bligede/bmt-avanza-iot-testing/ProjectDocs/BACKLOG.md

# BACKLOG: Alat Diagnostik CAN BMT

**Last updated:** 29 Sep 2026 WITA

Semua yang **belum bisa** atau **belum layak** dikerjakan sekarang, beserta apa
yang membukanya. Satu tempat, supaya tidak ada yang hilang di sela catatan.

Yang **sedang** dikerjakan dan yang **berikutnya** ada di
`agent-documentation/08-HANDOFF-CHECKLIST.md`. Pertanyaan yang menunggu jawaban
orang, bukan pekerjaan, tetap di berkas itu juga. Backlog ini isinya pekerjaan.

Status yang dipakai:

| Status | Artinya |
|---|---|
| **Siap** | tidak ada yang menghalangi, tinggal dikerjakan |
| **Menunggu akses** | butuh kendaraan, perangkat keras, atau jaringan tertentu |
| **Menunggu keputusan** | butuh jawaban operator BMT lebih dulu |
| **Ditahan sengaja** | bisa dikerjakan, tetapi sengaja tidak, dan alasannya ditulis |

---

## A. Beban perangkat dan kehilangan frame

Semuanya bersumber dari satu sebab yang sama: interupsi CAN berada di flash,
jadi setiap penulisan flash mematikan cache instruksi dan FIFO controller
meluap. Terukur 14,8 % hilang saat merekam ke flash, 0,0 % saat flash menganggur.
Rinciannya di `docs/evidence/00-umum/frame-loss.md`.

### B-01. Filter penerimaan hardware TWAI · **Ditahan sengaja**

Menyaring di controller, sebelum interupsi jalan, jadi frame yang tidak
diinginkan tidak menimbulkan kerja sama sekali.

Sudah diukur pada rekaman `gelora-004` yang sebenarnya:

| | |
|---|---|
| Lima identifier yang dipakai TDS | 26,3 % dari lalu lintas bus |
| Mask tunggal yang memuat kelimanya | meloloskan **13 dari 34** identifier |
| Beban setelah disaring | 36,4 % dari bus, jadi turun 63,6 % |

Mask TWAI memilih **pola bit**, bukan daftar, jadi tidak mungkin menyaring tepat
lima identifier. Itu sifat perangkat kerasnya, bukan kekurangan implementasi.

**Kenapa ditahan:** mematikan perekaman sudah memberi kehilangan **nol** tanpa
menyentuh kode sama sekali, sedangkan filter ini hanya memberi 63,6 % dan
membayarnya dengan rekaman yang **tidak lagi lengkap**. Satu-satunya kasus
pemakaiannya adalah sesi perekaman panjang yang memang hanya butuh sinyal TDS,
dan kasus itu belum ada.

**Yang membukanya:** kebutuhan merekam lama dengan hanya sinyal TDS, misalnya
uji ketahanan unit armada. Kalau dikerjakan, **wajib** ada cap di header berkas
rekaman yang menyatakan filter aktif dan mask-nya, supaya analisis berikutnya
tidak diam-diam mengira rekaman itu utuh.

### B-02. Format rekaman biner, bukan teks · **Siap**

Satu frame sekarang memakan sekitar 44 byte teks. Bentuk biner sekitar 17 byte,
jadi lalu lintas flash turun 2,6 kali dan jeda cache ikut turun sebanding.

Lebih baik daripada B-01 untuk kasus yang sama, karena **tidak membuang satu
frame pun**. Biayanya: format berubah, `capture_to_webcan.py` dan seluruh alat
pembaca harus menyesuaikan, dan berkas lama harus tetap terbaca.

**Kenapa belum:** belum ada sesi yang menuntutnya. Kalau pemetaan Wuling ternyata
menuntut perekaman flash yang panjang, ini yang dikerjakan lebih dulu, bukan B-01.

### B-03. Bangun ulang framework dengan `CONFIG_TWAI_ISR_IN_IRAM=y` · **Ditahan sengaja**

Perbaikan tepat di akar masalah: interupsi CAN pindah ke IRAM, dan penulisan
flash berhenti mengganggunya.

**Kenapa ditahan:** tidak bisa dengan paket Arduino siap pakai, perlu ESP-IDF
dengan Arduino sebagai komponen, dan itu mengubah seluruh cara build. Kalau arah
Orange Pi 5 (D-007) jadi, seluruh pekerjaan ini terbuang.

**Yang membukanya:** keputusan bahwa ESP32 tetap dipakai untuk jangka panjang.

### B-04. Slot microSD pada papan rev B · **Menunggu keputusan**

Menulis ke SD lewat SPI tidak mematikan cache instruksi, jadi interupsi CAN
tetap jalan. Sekaligus menghapus batas 12 MB.

**Yang membukanya:** keputusan rev A difabrikasi apa adanya atau langsung lompat
ke rev B. Rev A belum pernah difabrikasi, jadi masih sempat.

---

## B. Pemetaan kendaraan

### B-05. Pemetaan sinyal Wuling armada · **Menunggu akses**

Penghalang terbesar yang tersisa di seluruh project, dan satu-satunya yang
menghalangi `project-mdt-tds` bergerak.

Metodenya sudah terbukti, prosedurnya sudah tertulis, firmware tinggal ditambah
satu env kendaraan. Yang kurang **hanya akses ke kendaraannya**.

Persiapan ada di `08-HANDOFF-CHECKLIST.md` butir 3.

### B-06. Uji jalan Honda HR-V · **Menunggu akses**

Kandidat 8 Sep 2026 belum pernah diuji sambil berjalan, jadi statusnya sama
dengan status Gelora E sebelum 23 Sep: cocok di atas kertas, belum terbukti.

Bus HR-V sekitar 1.000 frame per detik, jadi kehilangan saat merekam ke flash
mencapai 22 sampai 26 persen. Sesi berikutnya **wajib** memakai aliran WiFi.

### B-07. Dokumen bukti untuk `gelora-002`, `gelora-003`, dan `gelora-005` · **Siap**

Tiga rekaman dari 22 September malam, 216.454 + 200.389 + 213.979 frame,
tersimpan di `captures/` tanpa dokumen bukti sama sekali. Sebagian angkanya
sudah dipakai di `frame-loss.md`, jadi rekamannya bukan sampah, hanya tidak
punya jejak.

Ketiganya tumpang tindih dan harus dibaca bersama: dua yang pertama dialirkan
ke laptop, yang ketiga ditulis ke flash alat. Itulah sisi kanan dan kiri dari
perbandingan 14,8 % lawan 0,0 %.

`gelora-005` baru ditarik 23 Sep 2026 dan **nyaris hilang**, lihat
`captures/gelora-005/RUN-SHEET.md`.

### B-08. Sinyal Gelora E yang belum selesai · **Siap**

| Yang belum selesai | Keadaannya |
|---|---|
| Nomor sel tertinggi `0x0CFF7D03` b2 | b2 = 44 sedangkan sel 3991 mV ada di posisi 46. Nilainya terbukti, penomorannya belum |
| SOH `0x0CFF7E03` b1 | tidak pernah berubah, jadi belum teruji sama sekali |
| Suhu controller `0x0CFF1601` b2 | **gugur**, tidak bergerak 47 menit termasuk saat arus 133 A. Perlu dicari ulang di identifier lain |
| Resistansi isolasi | tidak ada di 34 identifier mana pun. Kemungkinan hanya keluar lewat permintaan diagnostik, lihat B-14 |

### B-09. Rumus untuk frame multiplex · **Siap**

Tegangan 90 sel dan suhu 30 sensor berbentuk multiplex: satu byte indeks lalu
tiga nilai 16-bit. Mesin rumus di dashboard hanya bisa menyatakan satu frame
tunggal, jadi keduanya hanya bisa dinamai, tidak bisa ditampilkan sebagai angka
di panel Vehicle.

Untuk TDS ini belum penting. Untuk melihat ketidakseimbangan baterai di lapangan,
ini yang dibutuhkan.

---

## C. Dashboard

### B-10. Mode terang untuk dibaca di bawah matahari · **Siap**

Halaman sekarang gelap sepenuhnya. Di kabin terang siang hari, permukaan gelap
memantulkan lebih banyak daripada permukaan terang. Belum pernah diuji di
kendaraan pada siang hari, jadi ini dugaan, bukan keluhan terukur.

**Sebelum dikerjakan:** ukur dulu. Satu sesi siang hari sudah cukup untuk tahu
apakah ini masalah nyata.

### B-11. Panel Live Frames · **Menunggu keputusan**

Endpoint `/api/frames` ada, berjalan, dan menyajikan 60 frame terakhir, tetapi
**halaman tidak pernah memakainya**. Dua pilihan yang sama-sama sah: pakai
sebagai panel debug, atau hapus endpoint-nya karena kode yang tidak dipakai
tetap harus dirawat.

### B-12. Signal probe hanya menawarkan identifier yang tampil · **Ditahan sengaja**

Saat penyaring aktif, probe kehilangan identifier yang disembunyikan. Halaman
sudah mengatakannya dan menyarankan pindah ke All.

**Kenapa ditahan:** memberi probe daftar sendiri berarti dua sumber kebenaran di
satu halaman. Pindah ke All sudah cukup, dan lebih jujur.

---

## D. Perangkat keras

### B-13. Fabrikasi papan · **Menunggu keputusan**

Rev A sudah lengkap: skematik, netlist, dan BOM dibangkitkan dari satu berkas
sumber, diperiksa 12 aturan keselamatan oleh pemeriksa terpisah, diuji dengan
tiga cacat suntikan. Belum pernah difabrikasi. Lihat B-04 untuk rev B.

### B-14. Alat kedua yang bisa meminta data diagnostik · **Ditahan sengaja**

Nilai seperti resistansi isolasi tidak pernah disiarkan berkala, jadi alat ini
tidak akan pernah melihatnya. Menambah kemampuan meminta berarti **mengirim**,
dan itu membatalkan jaminan yang membuat alat ini boleh dipasang di kendaraan
orang lain.

**Kalau memang dibutuhkan, tempatnya alat kedua yang terpisah**, bukan alat ini.
Jaminan listen-only tidak pernah dilonggarkan untuk kenyamanan.

### B-15. Ukur suhu kotak di kabin terparkir · **Siap**

`FAN_ON_TEMP` dan `FAN_OFF_TEMP` di firmware armada masih nilai sementara
bertanda TODO VALIDASI TERMAL, karena belum ada yang mengukur kotak di mobil
terparkir di bawah matahari Bali. Alat ini punya DHT22 dan suhu die SoC, jadi ia
bisa menjawabnya sendiri dalam satu hari parkir.

---

## E. Kalau arah Orange Pi 5 jadi

Seluruh bagian ini berstatus **menunggu keputusan** D-007.

### B-16. Jaminan listen-only di SocketCAN · **Menunggu keputusan**

Yang paling penting dan paling mudah terlewat. Penegakan sekarang bersandar pada
mode controller TWAI, `#pragma GCC poison`, dan gate build. Di SocketCAN ketiganya
tidak berlaku apa adanya, dan penggantinya **harus dirancang, bukan diasumsikan**.
Tidak boleh lebih longgar daripada yang sekarang.

### B-17. Daya, kontak, dan mati mendadak · **Menunggu keputusan**

Orange Pi 5 tidak boleh mati mendadak saat kontak diputar. Butuh mematikan dengan
rapi, cadangan daya sesaat (supercapacitor atau UPS kecil), atau berkas rekaman yang tahan mati listrik.

### B-18. Waktu siap dan suhu kabin · **Menunggu keputusan**

Linux butuh puluhan detik untuk siap, sementara ESP32 ratusan milidetik. Batas
suhu kerja Orange Pi 5 juga lebih sempit, sedangkan kabin Bali bisa lewat 80 °C.

### B-19. Pindahkan alat analisis ke perangkat · **Menunggu keputusan**

Kalau jadi, Python, `cantools`, dan basis data bisa jalan di perangkat itu
sendiri, jadi pemetaan tidak lagi menuntut laptop ikut di mobil. Ini keuntungan
terbesarnya setelah hilangnya kehilangan frame.

---

## F. Proses dan kebersihan

### B-20. Rujukan `D-XXX` tanpa nama repositori · **Siap**

Rujukan di dalam kode dan `docs/` menyebut nomor telanjang, padahal `D-006`
berarti dua hal berbeda di dua repositori. Aturannya sudah ditulis di
`03-DECISIONS-LOG.md`, rujukan lamanya belum diperbaiki.

### B-21. Cadangan rekaman ke luar laptop · **SELESAI 23 Sep 2026**

Empat rekaman diarsipkan lengkap dengan sidik jari SHA-256 per berkas, lalu
diunggah operator BMT ke Google Drive: `gelora-002` (1,1 MB), `gelora-003`
(1,0 MB), `gelora-004` (8,0 MB), `gelora-005` (1,1 MB).

### B-24. Kosongkan flash alat supaya bisa merekam lagi · **SELESAI 23 Sep 2026**

Flash sempat 13,2 MB dari 14,3 MB terpakai dengan anggaran rekam **0 B**,
sehingga alat tidak bisa merekam apa pun.

Urutan yang ditempuh, dan urutan inilah yang penting: tarik seluruh isi ke
`captures/gelora-005`, bandingkan **64 sidik jari SHA-256** satu per satu dengan
isi alat sampai semuanya cocok, pastikan salinannya sudah ada di luar laptop,
baru hapus. Ukuran yang sama tidak membuktikan isi yang sama, dan yang dihapus
adalah satu-satunya pembanding yang tersisa.

Sesudahnya: 0 berkas di flash, penomoran segmen kembali ke `can-000`, dan
**delapan catatan identifier tetap utuh**, karena catatan memang disimpan
terpisah dari rekaman.

### B-25. Dua dashboard sekaligus di ESP32, lokal dulu · **TERBANGUN 28 Sep 2026, menunggu uji jalan**

**Instruksi Direktur BMT, 28 September 2026:** ESP32 menampilkan dua dashboard sekaligus
dan secara lokal dulu, yaitu (1) dashboard TDS SELARIDE yang baru dibuat, dan (2) dashboard
berisi semua data yang berhasil dipetakan pada pengujian DFSK Gelora E. Setelah itu berhasil,
baru ESP32 dicoba mengirim data ke server BMT.

Semua angka di bawah ini diukur di repo ini, bukan diperkirakan.

#### Ruang yang tersedia: cukup, dan bukan penghalang

| | Ukuran | Terpakai | Sisa |
|---|---|---|---|
| Partisi `app0` | 2.048 KB | ~800 KB firmware | **~1.200 KB** |
| LittleFS (`spiffs`) | 14.272 KB | rekaman CAN | belasan MB |

Halaman dashboard yang ada sekarang di-gzip ke flash saat build (`web/dist/index.html`,
77 KB mentah). Aset SELARIDE: teks (HTML, CSS, JS, font 31 KB) yang gzip-nya kecil, plus
**tiga gambar 136 KB** (foto mobil 70 KB, foto pengemudi 23 KB, logo 44 KB) yang tidak bisa
digzip lagi. Gambar-gambar itu masuk **LittleFS**, bukan partisi aplikasi: 136 KB dari
belasan MB, dan tidak menyentuh sisa ruang firmware sama sekali.

#### Yang belum ada, dan ini inti pekerjaannya

**Firmware ini belum punya decoder sinyal.** Ia perekam: menampilkan ID, frame mentah,
catatan per ID, GNSS, suhu. Kata "speed" di `src/` itu kecepatan GPS dari NMEA, bukan
kecepatan dari CAN. Jadi dua dashboard yang diminta sama-sama menunggu satu komponen baru
yang sama.

Urutan kerjanya, dan hanya yang pertama yang benar-benar baru:

1. **Decoder sinyal.** Tabel delapan pemetaan DFSK yang sudah terbukti (kecepatan,
   odometer, SOC, arus, tegangan pack, dua suhu baterai, putaran motor), sumbernya
   `docs/evidence/dfsk-gelora-e/gelora-004.md` dan `notes.tsv`. Menempel di jalur terima
   yang sudah ada, menyimpan nilai terakhir per sinyal, dan menyajikannya di `/api/signals`.
   Tidak menyentuh jalur kirim: alat ini tetap listen-only, dan aturan itu tidak dinegosiasikan.
2. **Dashboard 2, data terpetakan.** Sebagian besar sudah ada; yang ditambahkan panel nilai
   ter-decode di halaman yang sekarang. Murah begitu langkah 1 jadi.
3. **Dashboard 1, TDS SELARIDE.** Pindahkan `mdt-ui/` dari repo `project-mdt-tds`, ganti
   `mock.js` dengan umpan dari `/api/signals`. Aset teks ke flash, gambar ke LittleFS.
4. **Dua-duanya sekaligus.** Dua rute di server web yang sama: satu alat, dua alamat, bisa
   dibuka berbarengan dari dua tab atau dua ponsel.

#### Terjawab 28 Sep 2026, dan sudah dibangun

Ketiga keputusan di bawah dijawab operator pada hari yang sama: tombol mulai dan
akhiri dipencet manual dengan orangnya berperan sebagai penumpang, uji jalan
diulang di Gelora E, dan "sekaligus" berarti dua alamat di satu alat yang dibuka
dua gawai berbeda. Yang sudah ada di firmware sekarang:

| Bagian | Berkas | Catatan |
|---|---|---|
| Decoder sinyal | `src/SignalDecoder.{h,cpp}` | delapan pemetaan terbukti, disadap di task pembaca CAN, tidak menyentuh jalur kirim |
| Argo | `src/ArgoMeter.{h,cpp}` | jarak dari selisih odometer, tunggu dari frame kecepatan, keduanya tidak pernah ditagih bersamaan |
| Endpoint | `src/WebDashboard.cpp` | `GET /api/signals`, `POST /api/argo?action=start\|stop` |
| Layar argo | `web-argo/` | salinan halaman SELARIDE, mock diganti umpan alat, tombol trip jadi satu-satunya kontrol hidup |
| Aset | `tools/embed_web.py` | dua halaman plus empat berkas biner, 219 KB, semuanya di flash |

**Angka build:** flash 1.057.565 dari 2.097.152 byte, yaitu 50,4 persen. Sebelum
ini ~840 KB, jadi seluruh tambahan 219 KB itu asetnya. LittleFS tidak disentuh
sama sekali, dan itu disengaja: mengunggah image filesystem akan menghapus
rekaman CAN yang ada di sana.

Gerbang listen-only tetap lolos setelah semua perubahan ini.

Prosedurnya untuk besok ada di `docs/PROSEDUR-TEST-2-DASHBOARD.md`.

**Yang tersisa sebelum berangkat:** alat belum di-flash (port serial tidak
terdeteksi saat dibangun), dan catatan identifier harus dipasang lagi dengan
`tools/apply_notes.py` supaya panel Vehicle di dashboard teknis terisi.

#### Tiga keputusan yang menghalangi, dan semuanya milik Direktur

1. **Argo lokal butuh tombol mulai dan akhiri.** Tarif hanya menagih kilometer isi (D-011 di
   `project-mdt-tds`), dan alat ini tidak tahu ada penumpang atau tidak. Untuk demo lokal,
   satu tombol "Mulai argo / Akhiri" di halaman ESP32 membuat tarifnya nyata. Tanpa itu,
   tarifnya tetap data tiruan dan dashboard TDS-nya cuma tampilan.

   Kabar baiknya: begitu argo bisa dimulai, jarak isinya diambil dari **selisih odometer**
   yang sudah terbukti, bukan dari integral kecepatan. Itu lebih teliti daripada yang
   dipakai rangka MDT sekarang.
2. **Angka yang tampil adalah angka DFSK Gelora E, kendaraan uji.** Armada memakai Wuling
   dan belum pernah dipetakan. Konfirmasi bahwa demo lokal ini memang di kendaraan uji, dan
   bahwa tidak ada satu pun identifier di sini yang boleh disalin ke profil armada.
3. **"Sekaligus" itu dua alamat di satu alat, atau dua layar fisik?** Yang pertama sudah
   tercakup rencana ini. Yang kedua pekerjaan perangkat keras yang berbeda.

#### Yang perlu diukur setelah jadi, bukan diasumsikan

Status "Overworked" sebelumnya disebabkan perekaman yang menyala lagi sesudah boot, bukan
oleh halaman web. Tetap harus diukur ulang setelah dua dashboard hidup: `rx_overrun`,
`rx_missed`, dan beban CPU saat dua klien menarik `/api/state` dan `/api/signals` bersamaan.
Kalau naik, yang diturunkan dulu adalah laju polling, bukan isi layarnya.

#### Setelah ini baru kirim ke server

Kirim ke server BMT adalah fase berikutnya dan sudah punya tempatnya: arsitektur dua aliran
(D-008) dan pemilihan transport (T-13 di `project-mdt-tds`). Urutan yang diminta Direktur,
lokal dulu baru kirim, memang urutan yang benar: tanpa decoder, tidak ada yang layak dikirim.

### B-26. Kirim data alat ke server BMT · **Menunggu uji jalan**

Langkah yang Direktur tetapkan **setelah** dua dashboard terbukti jalan lokal (D-008):
alat mengirim data ke server BMT. Belum dikerjakan sama sekali, dan itu disengaja.

Yang membukanya: uji jalan 29 September lolos, artinya kedua halaman hidup di kendaraan
bergerak dan angkanya cocok dengan bukti.

Yang harus diputuskan sebelum satu baris pun ditulis, dan belum ada satu pun jawabannya:
alamat dan protokol server, siapa yang memegang kredensialnya, apa yang terjadi saat
jaringan putus di tengah jalan, dan apakah pengiriman boleh menunda tugas pembaca CAN.
Yang terakhir bukan pertanyaan gaya: pembaca CAN yang tertunda adalah frame yang hilang,
dan itu persis penyakit yang sudah pernah disembuhkan sekali di repo ini.

**Batas yang sudah pasti:** kunci server milik gerbang pembayaran tidak pernah boleh ada
di perangkat kendaraan.

### B-27. Flash firmware dua dashboard ke alat · **SELESAI 28 Sep 2026**

Di-flash lewat USB (COM6) memakai `pio run -t upload`, bukan `uploadfs`. Partisi
LittleFS tidak disentuh. Hash `firmware.bin` terverifikasi saat upload, kedua
halaman terbukti menjawab lewat WiFi. Rincian di D-010.

Catatan identifier **tidak perlu dipasang ulang**: delapan catatan bertahan di
`/notes/GELORAE-TEST-01` melewati proses flash aplikasi, karena catatan tinggal
di LittleFS dan flashing aplikasi tidak menyentuh partisi itu.

### B-28. Tarik 13,3 MB rekaman lama dari flash alat · **Siap**

Ditemukan saat sesi flashing 28 September: 60 berkas di `/capture/`, sisa ruang
hanya 421 KB dari 14.614.528 B total. Empat berkas terakhir (`can-055` sampai
`can-058`) 0 byte, artinya sudah ada sesi perekaman yang gagal karena kehabisan
tempat sebelum ditemukan.

`clearcaptures` **belum dijalankan**. Rekaman yang belum dicadangkan tidak boleh
dihapus atas inisiatif sendiri, dan repo ini punya aturan yang sama untuk bukti
lama: raw evidence immutable (D-015, `bmt-can-bus-telemetry`).

Alat sekarang di jaringan (D-010), jadi menariknya lewat `GET /api/captures` atau
endpoint unduh serupa jauh lebih cepat daripada lewat serial. Setelah ditarik dan
diverifikasi, `clearcaptures` baru boleh dijalankan.

**Ini bukan penghalang untuk uji jalan hari ini** kalau perekaman dimatikan dulu
(`capture off`), tetapi **menghalangi total** sesi pemetaan berikutnya begitu
421 KB yang tersisa habis, karena perekaman menyala otomatis tiap boot dan akan
langsung gagal menulis.

### B-22. Pastikan token GitHub yang bocor sudah dicabut · **Siap**

Token milik akun `wira97-tech` tercetak ke keluaran terminal pada 22 Sep 2026.
Jalur push sekarang sudah memakai kredensial bernama dan keluarannya disaring,
tetapi belum ada yang memastikan token lamanya benar-benar dicabut.

### B-23. Sampaikan temuan baterai ke pemilik kendaraan · **Siap**

Paket Gelora E tidak seimbang, sel terendah 200 sampai 260 mV di bawah mayoritas,
dan selisihnya melebar antara 22 dan 23 September. Tidak terlihat dari layar
mobil. Begitu disampaikan, catat di `06-COMMUNICATION-LOG.md`.
