bligede/bmt-avanza-iot-testing/ProjectDocs/agent-documentation/06-COMMUNICATION-LOG.md

# 06: Communication log

Timeline percakapan dengan pihak luar, urut kronologis, terbaru di bawah.

## Kenapa berkas ini kosong

Project ini internal PT Bali Mikro Teknologi dan **tidak punya klien eksternal**. Lihat
`01-CONTEXT-PROJECT.md`. Keputusan diambil operator BMT dan tercatat di
`03-DECISIONS-LOG.md` lengkap dengan kutipan literal, jadi tidak ada percakapan eksternal
yang perlu dikronologikan di sini.

Berkas ini kosong dengan sengaja, bukan karena terlupa.

## Kapan berkas ini mulai dipakai

Tiga keadaan yang mengubahnya:

1. **Pemilik kendaraan uji jadi pihak yang perlu dilapori.** Sesi 22 dan 23 September
   menemukan paket baterai Gelora E tidak seimbang, dan temuan semacam itu perlu
   disampaikan ke pemilik kendaraan. Begitu percakapan itu terjadi, catat di sini.
2. **Armada Baswara dikelola bersama pihak luar.** Jalur SELARIDE atau
   Baswara-Transtrack pernah muncul di catatan surat BMT. Kalau itu terjadi, status
   project berubah dan kanal komunikasinya mulai dicatat.
3. **Hasil project ini diserahkan ke pihak ketiga** dalam bentuk dokumen atau presentasi.

Sampai salah satunya terjadi, biarkan berkas ini apa adanya. Pengisiannya lewat skill
`bmt-communication-log`.
