bligede/bmt-avanza-iot-testing/hardware/bmt-can-logger.kicad_sch

## KiCad design hardware/bmt-can-logger.kicad_sch (2026-09-19)

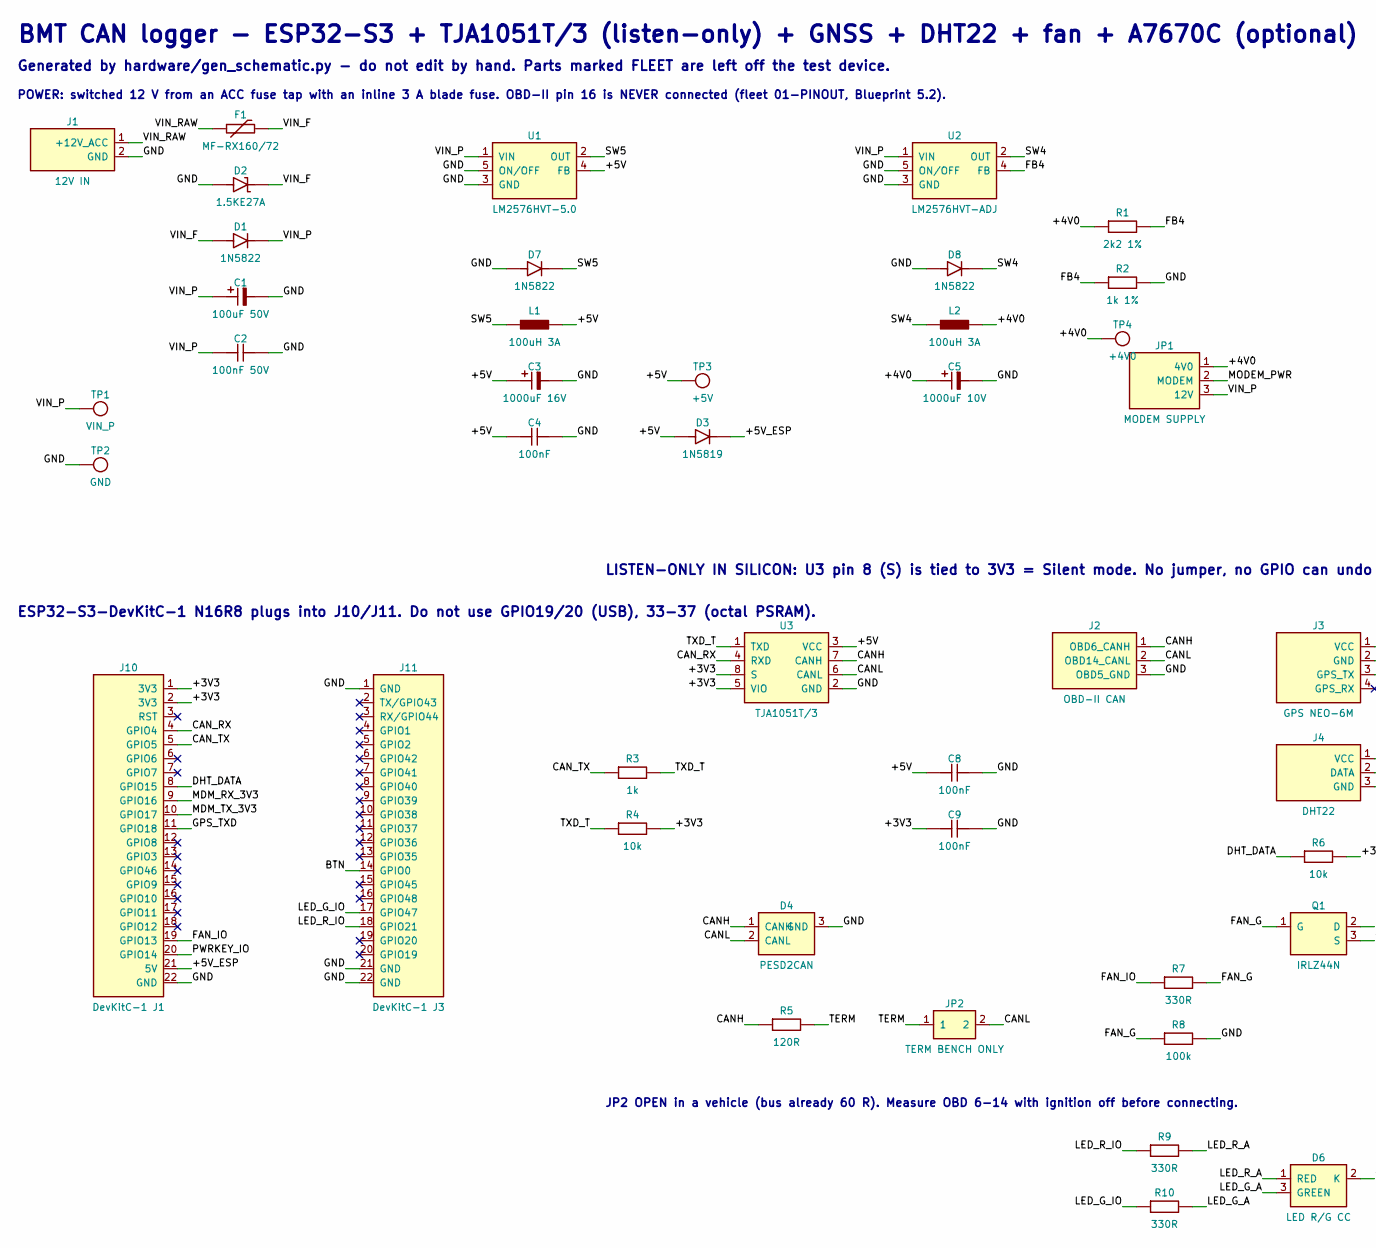
[picture p4: schematic bmt-can-logger.kicad_sch, part in row 1, column 1]

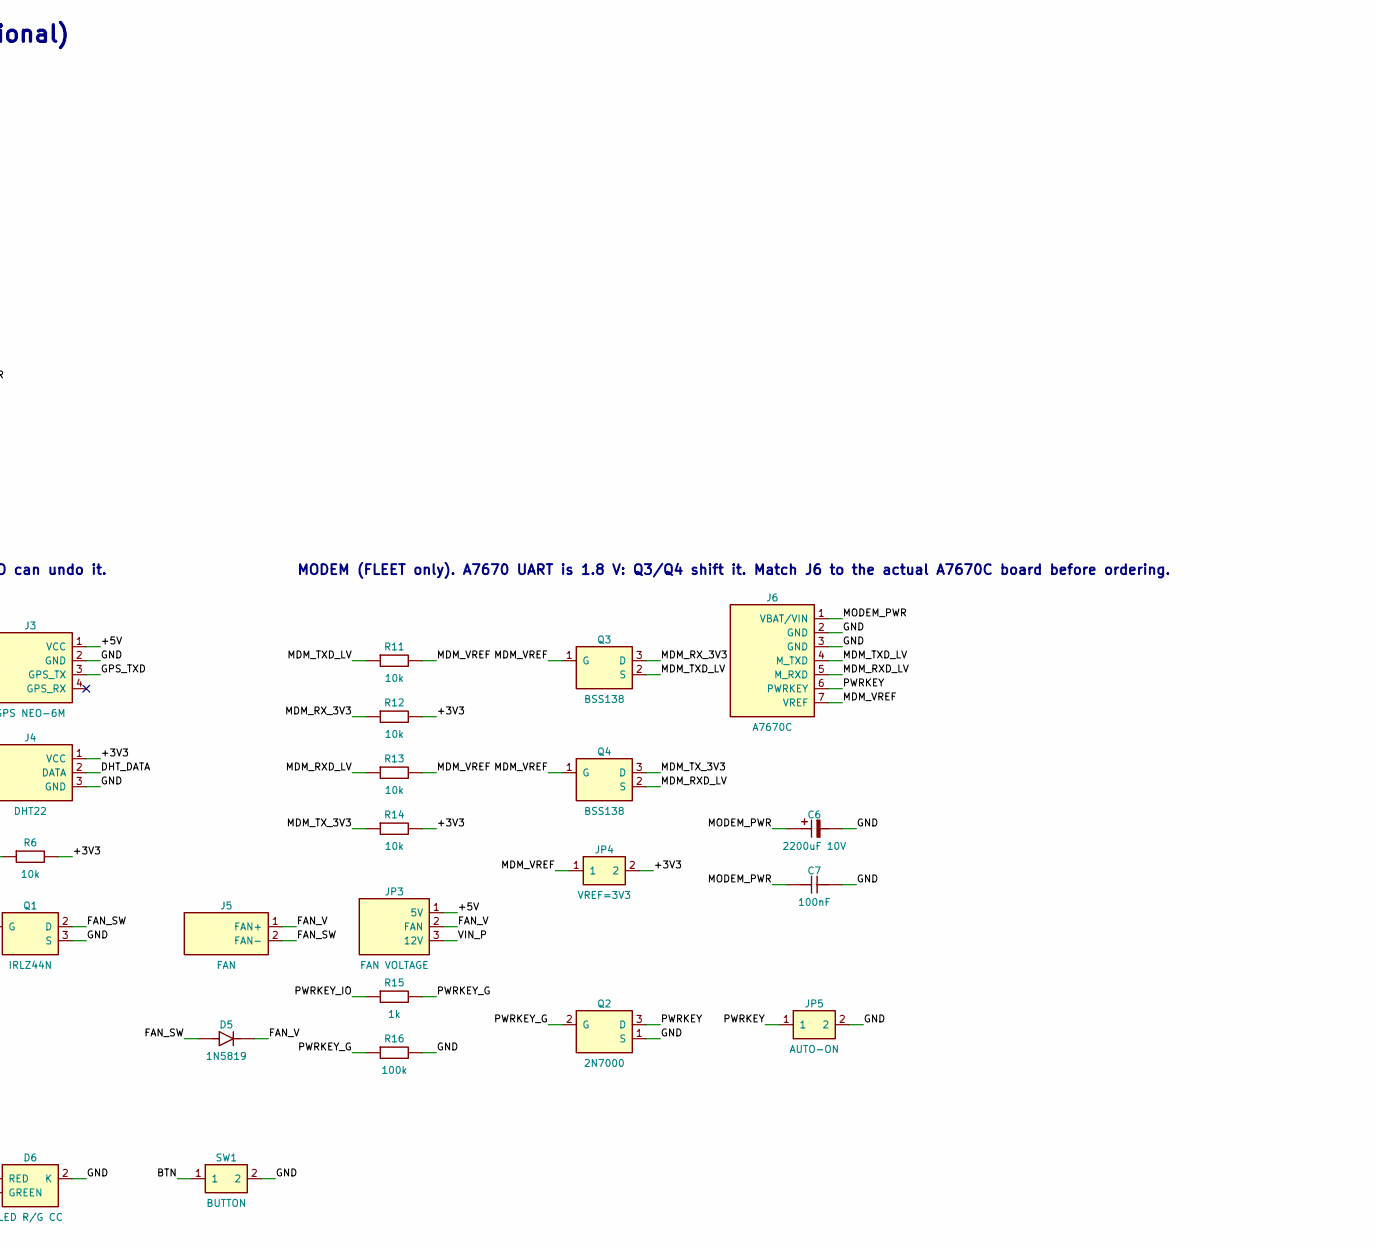
[picture p5: schematic bmt-can-logger.kicad_sch, part in row 1, column 2]

Parts:
C1: 100uF 50V; CP_Radial_D8.0mm_P3.50mm
C2: 100nF 50V; C_Disc_D5.0mm_W2.5mm_P5.00mm
C3: 1000uF 16V; CP_Radial_D10.0mm_P5.00mm
C4, C7, C8, C9: 100nF; C_Disc_D5.0mm_W2.5mm_P5.00mm
C5: 1000uF 10V; CP_Radial_D10.0mm_P5.00mm
C6: 2200uF 10V; CP_Radial_D12.5mm_P5.00mm
D1, D7, D8: 1N5822; D_DO-201AD_P15.24mm_Horizontal; MPN 1N5822
D2: 1.5KE27A; D_DO-201_P15.24mm_Horizontal; MPN Littelfuse 1.5KE27A
D3, D5: 1N5819; D_DO-41_SOD81_P10.16mm_Horizontal; MPN 1N5819
D4: PESD2CAN; SOT-23; MPN Nexperia PESD2CAN
D6: LED R/G CC; LED_D5.0mm-3
F1: MF-RX160/72; MPN Bourns MF-RX160/72
J1: 12V IN; TerminalBlock_Phoenix_MKDS-1,5-2-5.08_1x02_P5.08mm_Horizont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; MPN Phoenix MKDS 1,5/2-5.08 (or any 5.08 mm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
J2: OBD-II CAN; TerminalBlock_Phoenix_MKDS-1,5-3-5.08_1x03_P5.08mm_Horizont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; MPN Phoenix MKDS 1,5/3-5.08
J3: GPS NEO-6M; PinHeader_1x04_P2.54mm_Vertical
J4: DHT22; PinHeader_1x03_P2.54mm_Vertical
J5: FAN; PinHeader_1x02_P2.54mm_Vertical
J6: A7670C; PinHeader_1x07_P2.54mm_Vertical
J10: DevKitC-1 J1; PinSocket_1x22_P2.54mm_Vertical; MPN 2.54 mm female socket 1x22
J11: DevKitC-1 J3; PinSocket_1x22_P2.54mm_Vertical; MPN 2.54 mm female socket 1x22
JP1: MODEM SUPPLY; PinHeader_1x03_P2.54mm_Vertical
JP2: TERM BENCH ONLY; PinHeader_1x02_P2.54mm_Vertical
JP3: FAN VOLTAGE; PinHeader_1x03_P2.54mm_Vertical
JP4: VREF=3V3; PinHeader_1x02_P2.54mm_Vertical
JP5: AUTO-ON; PinHeader_1x02_P2.54mm_Vertical
L1, L2: 100uH 3A
Q1: IRLZ44N; TO-220-3_Vertical; MPN IRLZ44N
Q2: 2N7000; TO-92_Inline; MPN 2N7000
Q3, Q4: BSS138; SOT-23; MPN BSS138
R1: 2k2 1%; R_Axial_DIN0207_L6.3mm_D2.5mm_P10.16mm_Horizontal
R2: 1k 1%; R_Axial_DIN0207_L6.3mm_D2.5mm_P10.16mm_Horizontal
R3, R15: 1k; R_Axial_DIN0207_L6.3mm_D2.5mm_P10.16mm_Horizontal
R4, R6, R11, R12, R13, R14: 10k; R_Axial_DIN0207_L6.3mm_D2.5mm_P10.16mm_Horizontal
R5: 120R; R_Axial_DIN0207_L6.3mm_D2.5mm_P10.16mm_Horizontal
R7, R9, R10: 330R; R_Axial_DIN0207_L6.3mm_D2.5mm_P10.16mm_Horizontal
R8, R16: 100k; R_Axial_DIN0207_L6.3mm_D2.5mm_P10.16mm_Horizontal
SW1: BUTTON; SW_PUSH_6mm
TP1: VIN_P; TestPoint_THTPad_D2.0mm_Drill1.0mm
TP2: GND; TestPoint_THTPad_D2.0mm_Drill1.0mm
TP3: +5V; TestPoint_THTPad_D2.0mm_Drill1.0mm
TP4: +4V0; TestPoint_THTPad_D2.0mm_Drill1.0mm
U1: LM2576HVT-5.0; TO-220-5_P3.4x3.7mm_StaggerOdd_Lead3.8mm_Vertical; MPN TI LM2576HVT-5.0
U2: LM2576HVT-ADJ; TO-220-5_P3.4x3.7mm_StaggerOdd_Lead3.8mm_Vertical; MPN TI LM2576HVT-ADJ
U3: TJA1051T/3; SOIC-8_3.9x4.9mm_P1.27mm; MPN NXP TJA1051T/3

Connections:
+3V3: C9.1, J4.1 (VCC), J10.1 (3V3), J10.2 (3V3), JP4.2, R4.2, R6.2, R12.2, R14.2, U3.5 (VIO), U3.8 (S)
+4V0: C5.1, JP1.1 (4V0), L2.2, R1.1, TP4.1
+5V: C3.1, C4.1, C8.1, D3.2 (A), J3.1 (VCC), JP3.1 (5V), L1.2, TP3.1, U1.4 (FB), U3.3 (VCC)
+5V_ESP: D3.1 (K), J10.21 (5V)
BTN: J11.14 (GPIO0), SW1.1
CANH: D4.1 (CANH), J2.1 (OBD6_CANH), R5.1, U3.7 (CANH)
CANL: D4.2 (CANL), J2.2 (OBD14_CANL), JP2.2, U3.6 (CANL)
CAN_RX: J10.4 (GPIO4), U3.4 (RXD)
CAN_TX: J10.5 (GPIO5), R3.1
DHT_DATA: J4.2 (DATA), J10.8 (GPIO15), R6.1
FAN_G: Q1.1 (G), R7.2, R8.1
FAN_IO: J10.19 (GPIO13), R7.1
FAN_SW: D5.2 (A), J5.2 (FAN-), Q1.2 (D)
FAN_V: D5.1 (K), J5.1 (FAN+), JP3.2 (FAN)
FB4: R1.2, R2.1, U2.4 (FB)
GND: C1.2, C2.2, C3.2, C4.2, C5.2, C6.2, C7.2, C8.2, C9.2, D2.2 (A), D4.3 (GND), D6.2 (K), D7.2 (A), D8.2 (A), J1.2 (GND), J2.3 (OBD5_GND), J3.2 (GND), J4.3 (GND), J6.2 (GND), J6.3 (GND), J10.22 (GND), J11.1 (GND), J11.21 (GND), J11.22 (GND), JP5.2, Q1.3 (S), Q2.1 (S), R2.2, R8.2, R16.2, SW1.2, TP2.1, U1.3 (GND), U1.5 (ON/OFF), U2.3 (GND), U2.5 (ON/OFF), U3.2 (GND)
GPS_TXD: J3.3 (GPS_TX), J10.11 (GPIO18)
LED_G_A: D6.3 (GREEN), R10.2
LED_G_IO: J11.17 (GPIO47), R10.1
LED_R_A: D6.1 (RED), R9.2
LED_R_IO: J11.18 (GPIO21), R9.1
MDM_RXD_LV: J6.5 (M_RXD), Q4.2 (S), R13.1
MDM_RX_3V3: J10.9 (GPIO16), Q3.3 (D), R12.1
MDM_TXD_LV: J6.4 (M_TXD), Q3.2 (S), R11.1
MDM_TX_3V3: J10.10 (GPIO17), Q4.3 (D), R14.1
MDM_VREF: J6.7 (VREF), JP4.1, Q3.1 (G), Q4.1 (G), R11.2, R13.2
MODEM_PWR: C6.1, C7.1, J6.1 (VBAT/VIN), JP1.2 (MODEM)
PWRKEY: J6.6 (PWRKEY), JP5.1, Q2.3 (D)
PWRKEY_G: Q2.2 (G), R15.2, R16.1
PWRKEY_IO: J10.20 (GPIO14), R15.1
SW4: D8.1 (K), L2.1, U2.2 (OUT)
SW5: D7.1 (K), L1.1, U1.2 (OUT)
TERM: JP2.1, R5.2
TXD_T: R3.2, R4.1, U3.1 (TXD)
VIN_F: D1.2 (A), D2.1 (K), F1.2
VIN_P: C1.1, C2.1, D1.1 (K), JP1.3 (12V), JP3.3 (12V), TP1.1, U1.1 (VIN), U2.1 (VIN)
VIN_RAW: F1.1, J1.1 (+12V_ACC)

Notes on the sheet:
BMT CAN logger - ESP32-S3 + TJA1051T/3 (listen-only) + GNSS + DHT22 + fan + A7670C (optional)
Generated by hardware/gen_schematic.py - do not edit by hand. Parts marked FLEET are left off the test device.
POWER: switched 12 V from an ACC fuse tap with an inline 3 A blade fuse. OBD-II pin 16 is NEVER connected (fleet 01-PINOUT, Blueprint 5.2).
ESP32-S3-DevKitC-1 N16R8 plugs into J10/J11. Do not use GPIO19/20 (USB), 33-37 (octal PSRAM).
LISTEN-ONLY IN SILICON: U3 pin 8 (S) is tied to 3V3 = Silent mode. No jumper, no GPIO can undo it.
JP2 OPEN in a vehicle (bus already 60 R). Measure OBD 6-14 with ignition off before connecting.
MODEM (FLEET only). A7670 UART is 1.8 V: Q3/Q4 shift it. Match J6 to the actual A7670C board before ordering.
